i-Saac-IV/FFT-spectrum-analyser/images/DSC00164.jpg

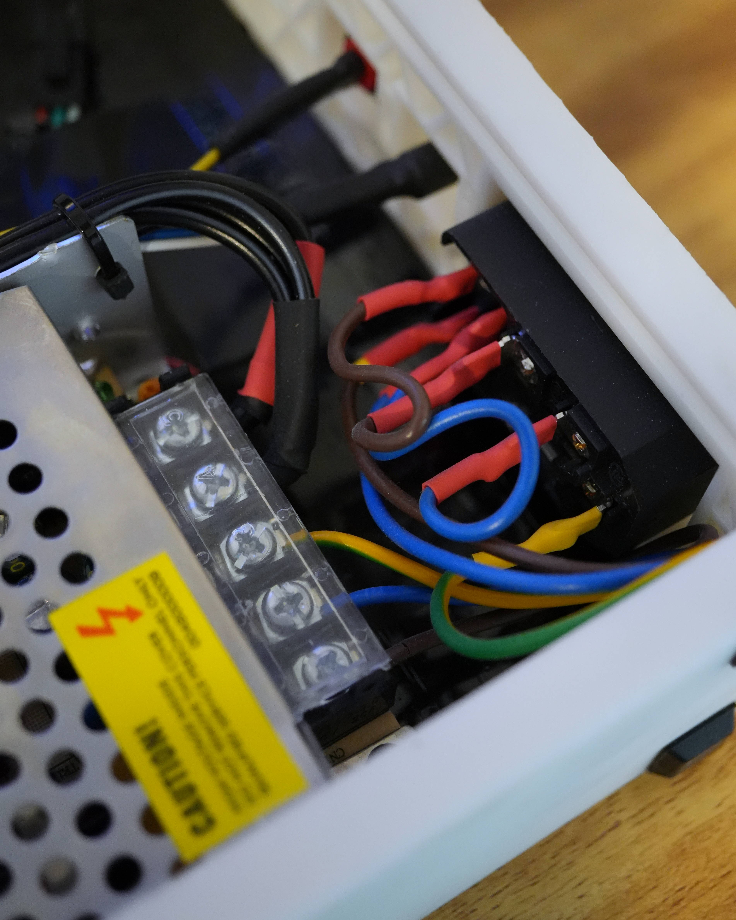
images/DSC00164.jpg
