i-Saac-IV/FFT-spectrum-analyser/images/DSC00175.jpg

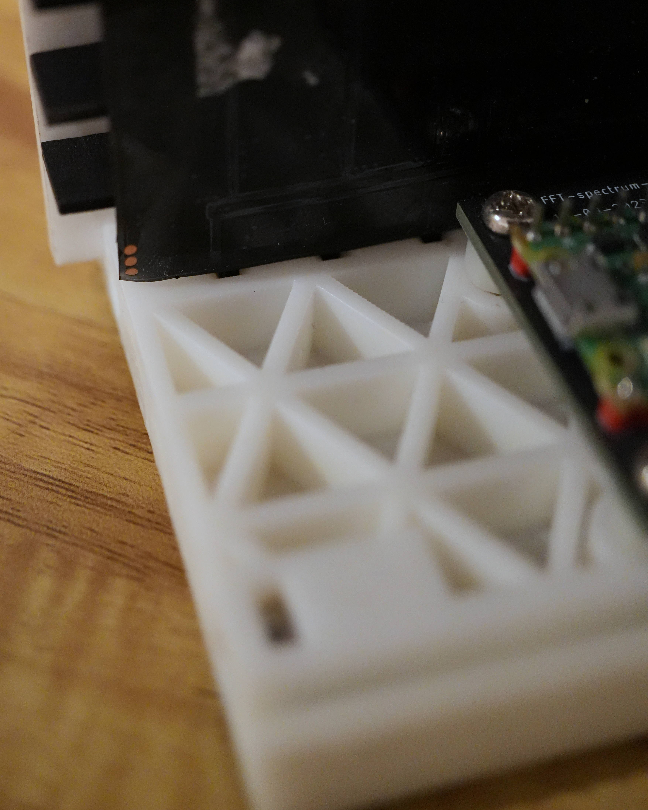
images/DSC00175.jpg
