i-Saac-IV/FFT-spectrum-analyser/images/DSC00184.jpg

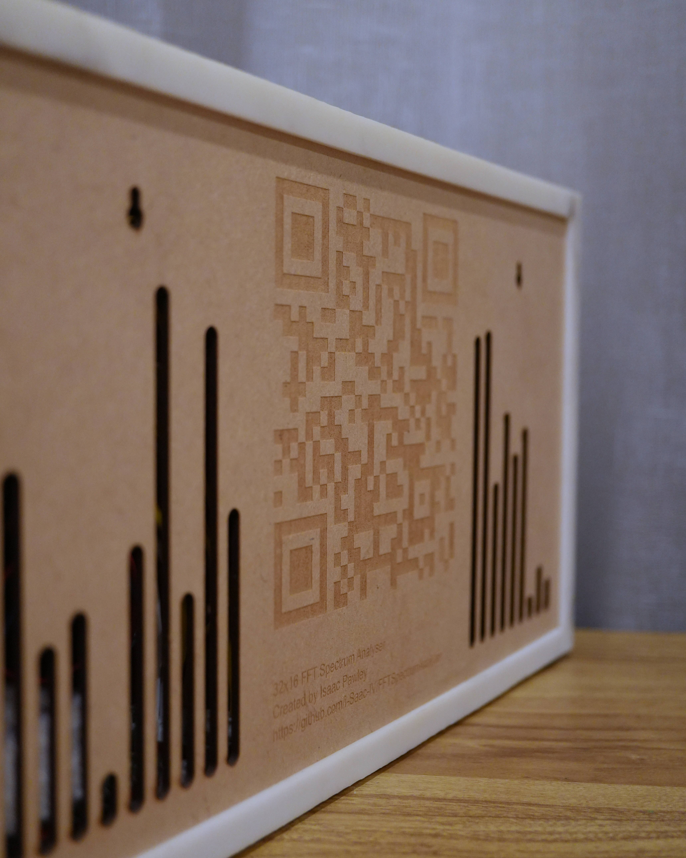
images/DSC00184.jpg
